lagnajeet/Odroid-GameXUbe/Images/IMG_20181231_205404.jpg

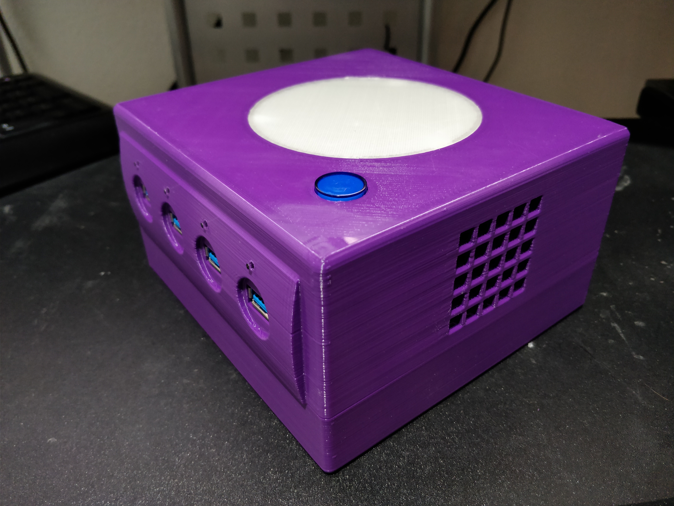
Images/IMG_20181231_205404.jpg
