lagnajeet/Odroid-GameXUbe/Images/IMG_20181231_205423.jpg

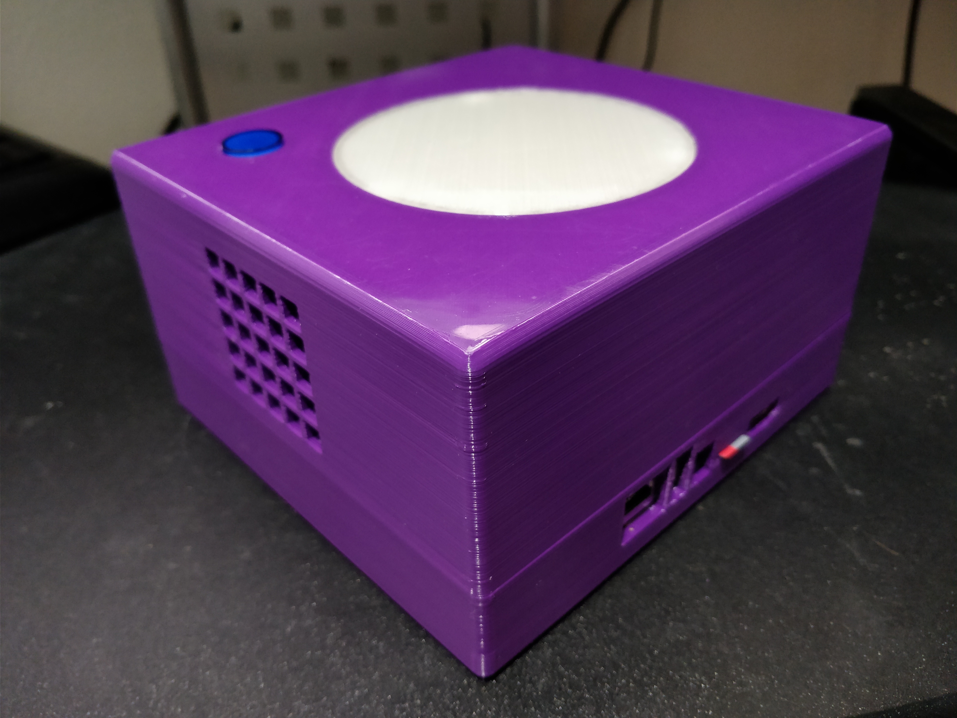
Images/IMG_20181231_205423.jpg
