lagnajeet/Odroid-GameXUbe/Images/IMG_20181231_205443.jpg

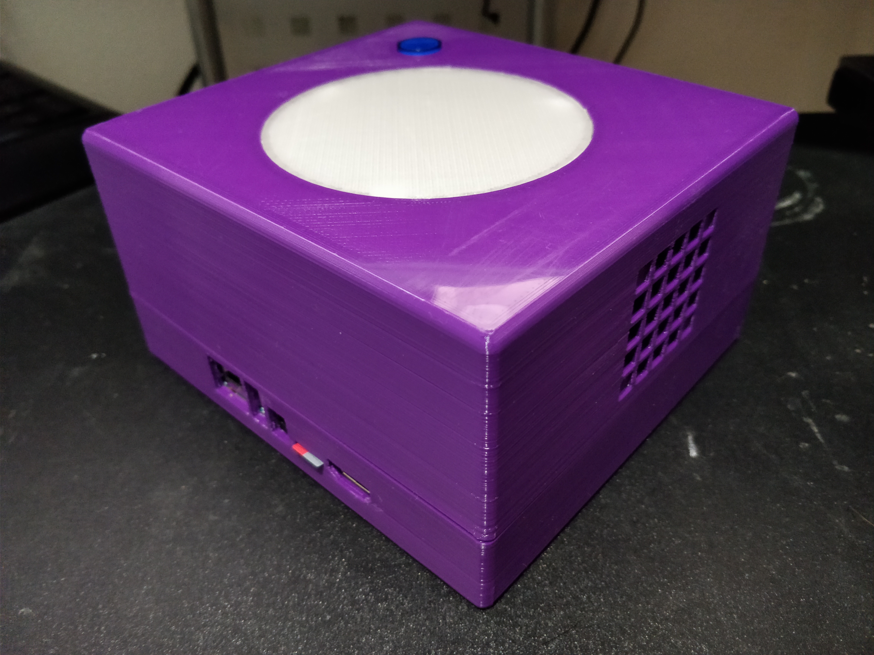
Images/IMG_20181231_205443.jpg
