lagnajeet/Odroid-GameXUbe/Images/IMG_20181231_205457.jpg

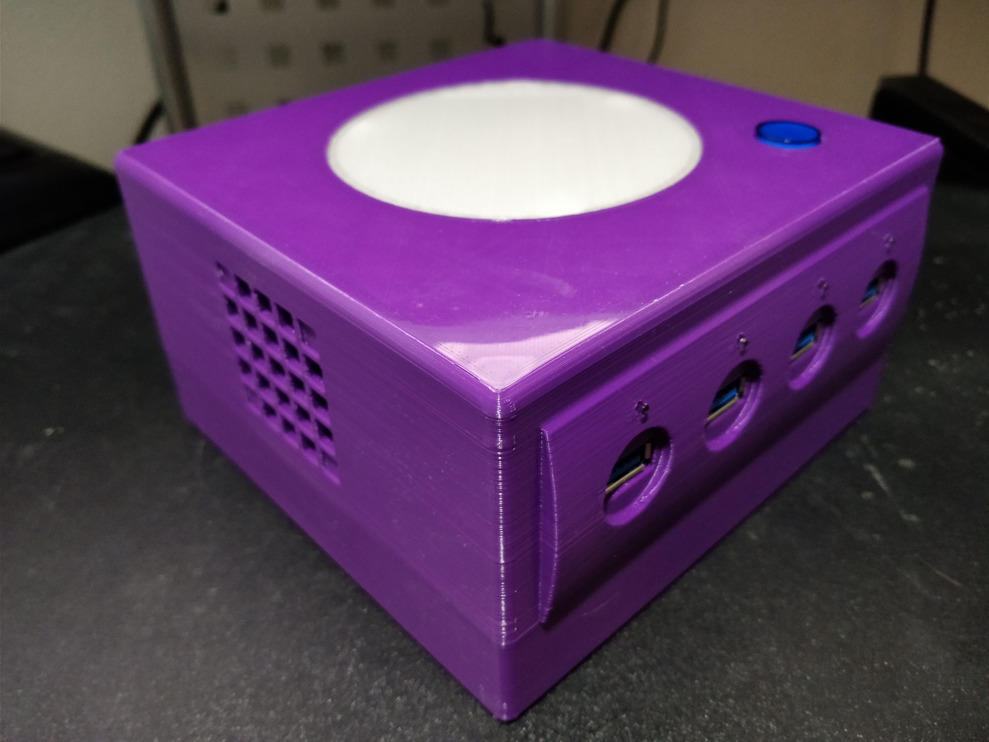
Images/IMG_20181231_205457.jpg
